jonymorse/SensorFusion-Models/outputs/previews/pt3-faceplate-alignment-concept.png

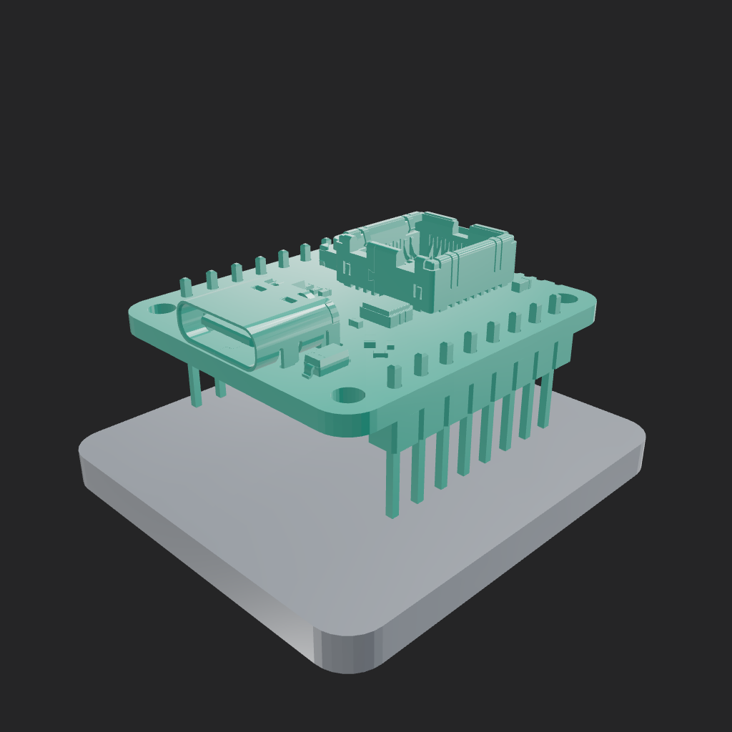
outputs/previews/pt3-faceplate-alignment-concept.png
