jonymorse/SensorFusion-Models/outputs/previews/pt3-front.png

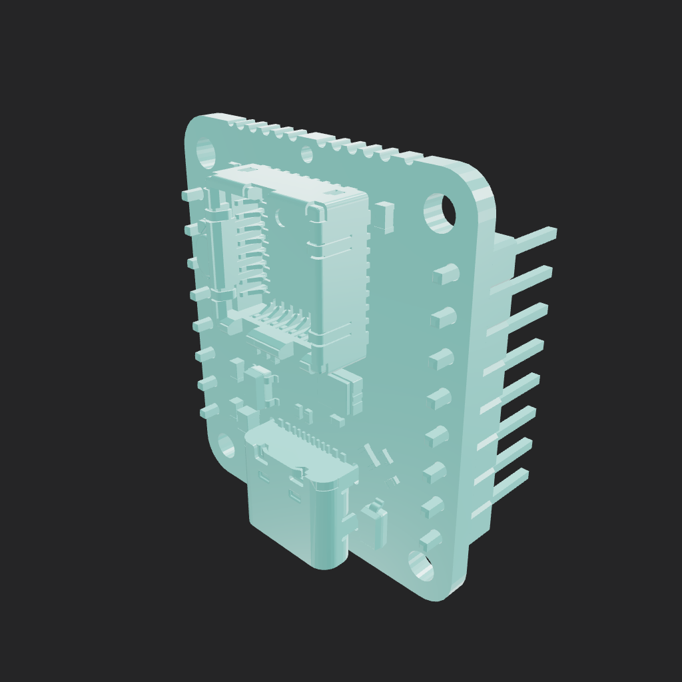
outputs/previews/pt3-front.png
