jonymorse/SensorFusion-Models/outputs/previews/pt3-right.png

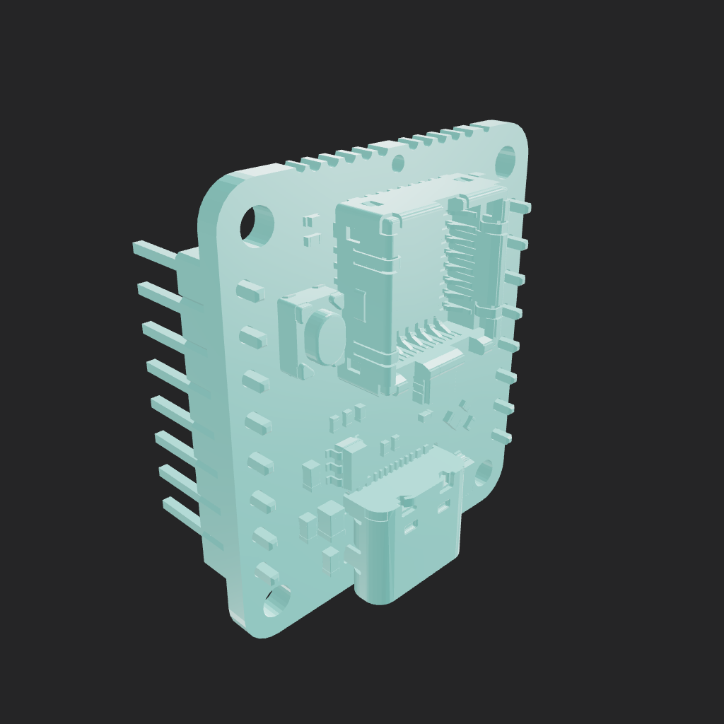
outputs/previews/pt3-right.png
