jonymorse/SensorFusion-Models/outputs/previews/pt3-top.png

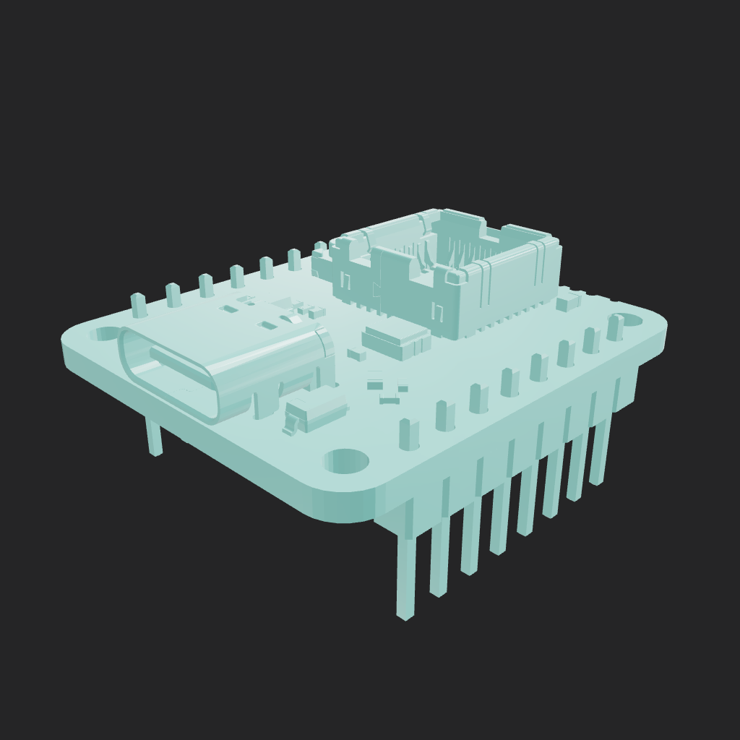
outputs/previews/pt3-top.png
