jonymorse/SensorFusion-Models/outputs/previews/purethermal-left.png

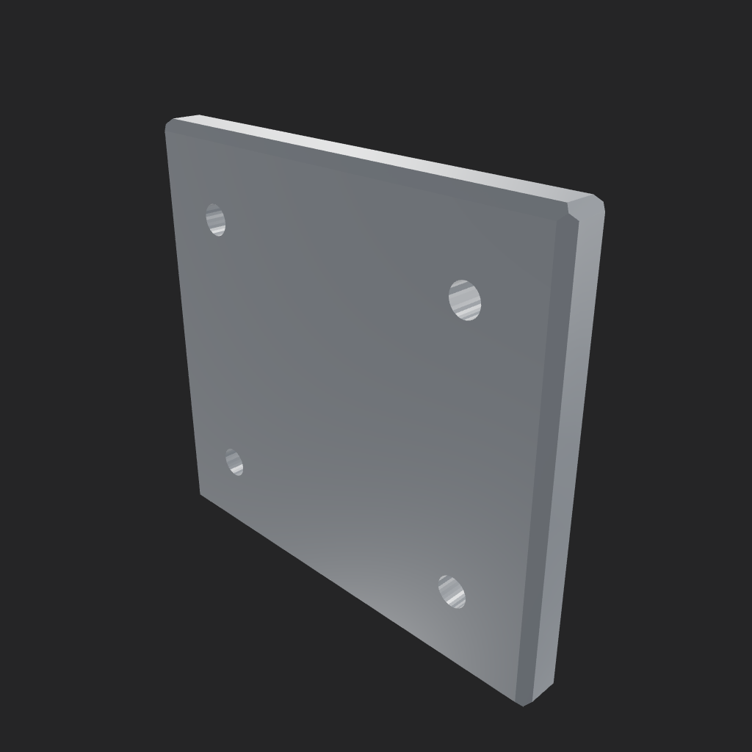
outputs/previews/purethermal-left.png
