jonymorse/SensorFusion-Models/outputs/previews/purethermal-tray-fresh.png

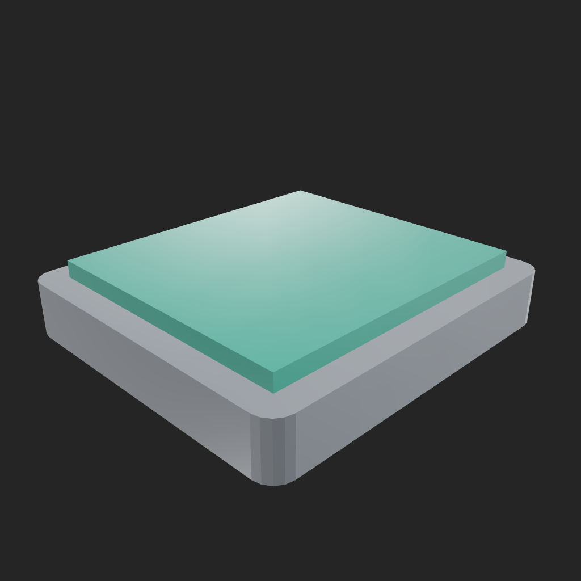
outputs/previews/purethermal-tray-fresh.png
