jonymorse/SensorFusion-Models/outputs/previews/purethermal-tray-scallop.png

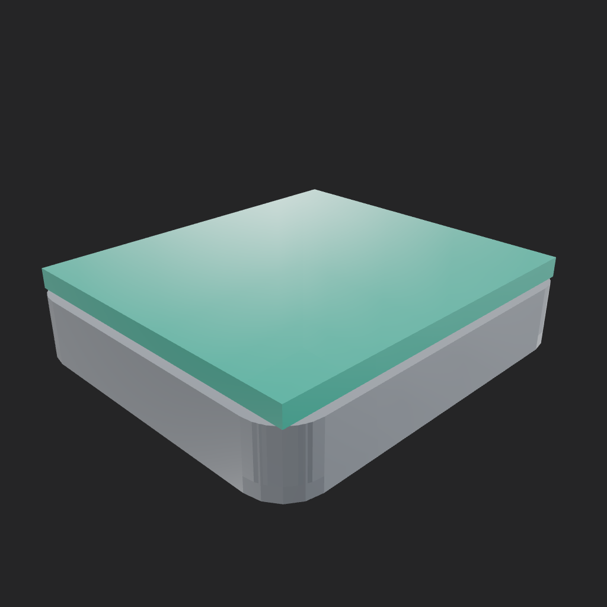
outputs/previews/purethermal-tray-scallop.png
