jonymorse/SensorFusion-Models/portfolio/assembly-viewer/models/03_pt3_slot_retainer.obj

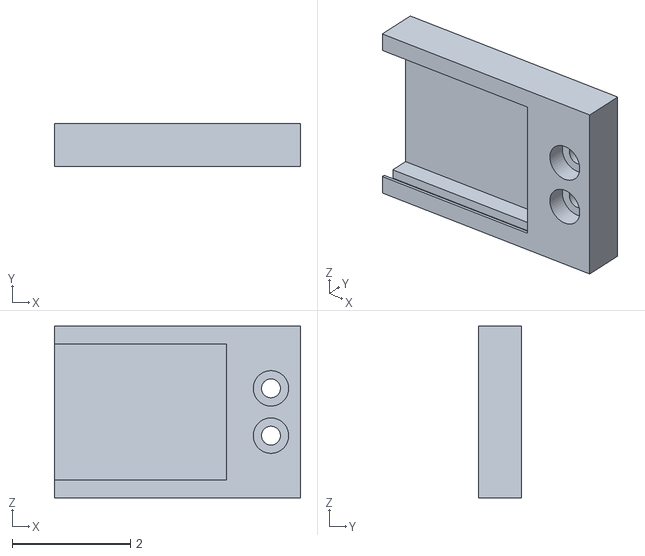
[picture p22: CAD file, 2026-07-29]
portfolio/assembly-viewer/models/03_pt3_slot_retainer.obj
4.16 x 0.72 x 2.91
