jonymorse/SensorFusion-Models/portfolio/assembly-viewer/models/08_quest_mount.obj

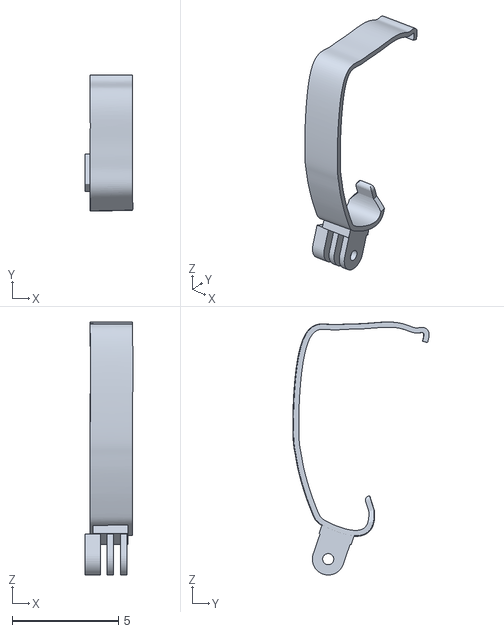
[picture p23: CAD file, 2026-07-29]
portfolio/assembly-viewer/models/08_quest_mount.obj
2.24 x 6.43 x 11.9
