jonymorse/SensorFusion-Models/portfolio/assembly-viewer/models/09_quest_3s.obj

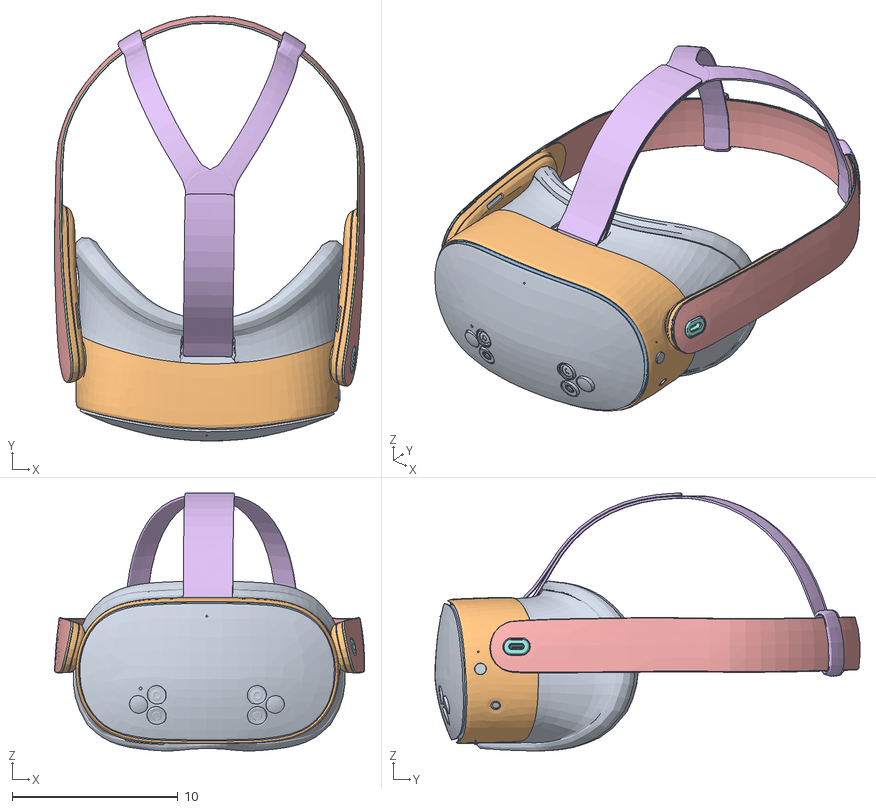
[picture p24: CAD file, 2026-07-29]
portfolio/assembly-viewer/models/09_quest_3s.obj
18.7 x 25.7 x 15.6
MeshBody12
MeshBody13
MeshBody14
MeshBody15
MeshBody16
MeshBody17
MeshBody18
MeshBody19
MeshBody20
