jonymorse/SensorFusion-Models/outputs/previews/purethermal-tray-with-pt3-step.png

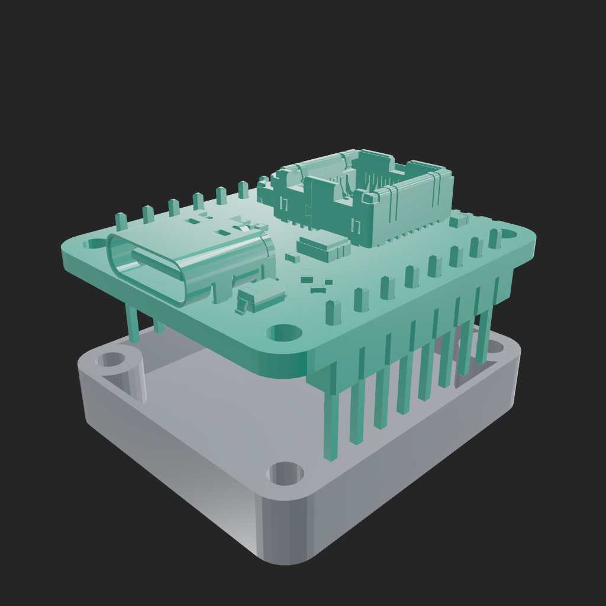
outputs/previews/purethermal-tray-with-pt3-step.png
