jonymorse/SensorFusion-Models/portfolio/assembly-viewer/dossier/integration/pt3-thermal.png

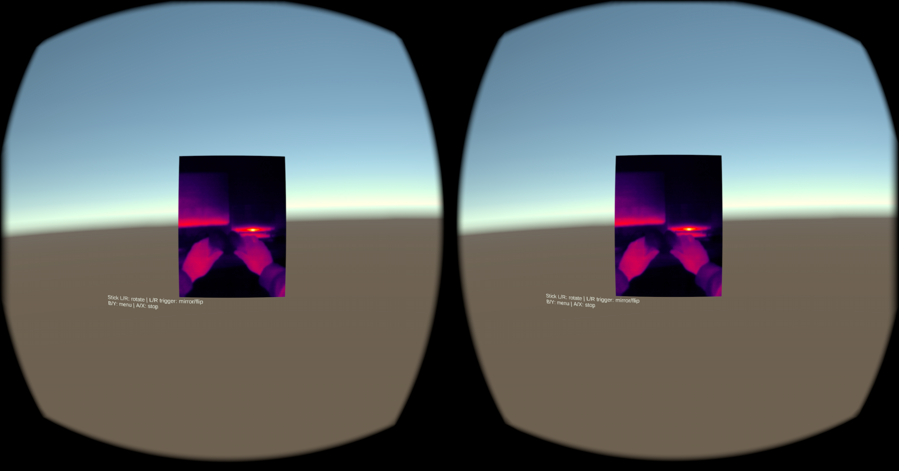
portfolio/assembly-viewer/dossier/integration/pt3-thermal.png
