jonymorse/SensorFusion-Models/portfolio/assembly-viewer/dossier/integration/realsense-depth.png

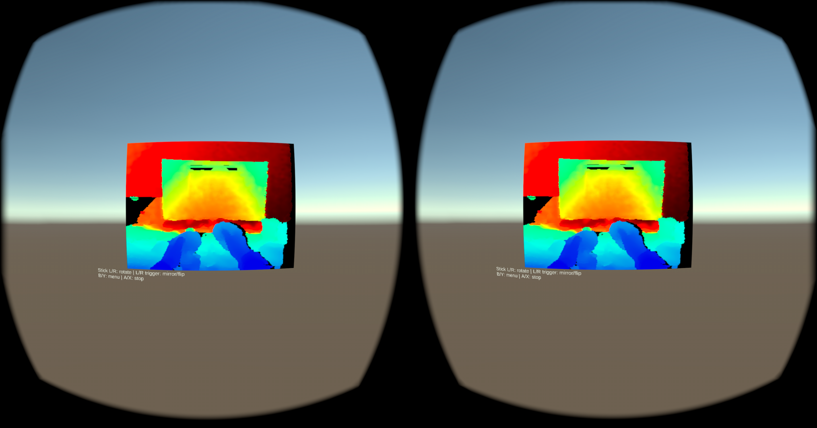
portfolio/assembly-viewer/dossier/integration/realsense-depth.png
