jonymorse/SensorFusion-Models/portfolio/assembly-viewer/dossier/integration/sensor-menu.jpg

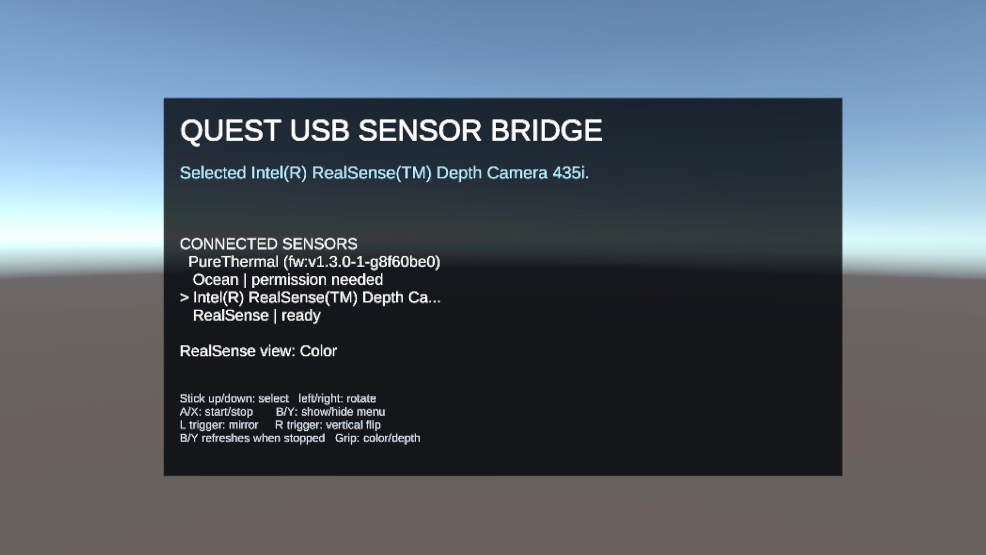
portfolio/assembly-viewer/dossier/integration/sensor-menu.jpg
