jonymorse/SensorFusion-Models/portfolio/assembly-viewer/dossier/quest-3s-reference-preview.png

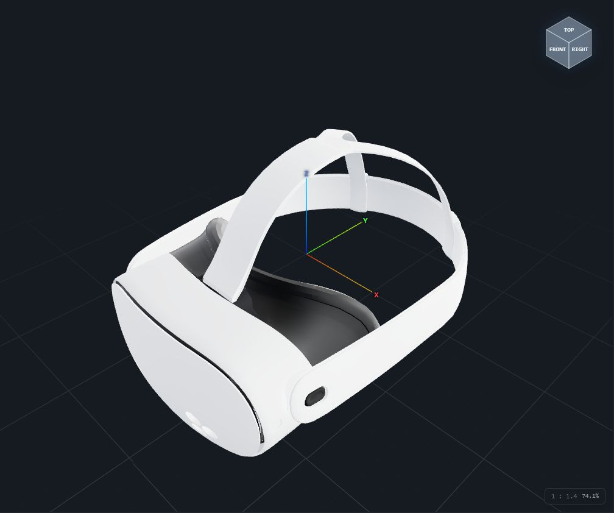
portfolio/assembly-viewer/dossier/quest-3s-reference-preview.png
