jonymorse/SensorFusion-Models/portfolio/assembly-viewer/dossier/quest-captures/latest-unity-capture.jpg

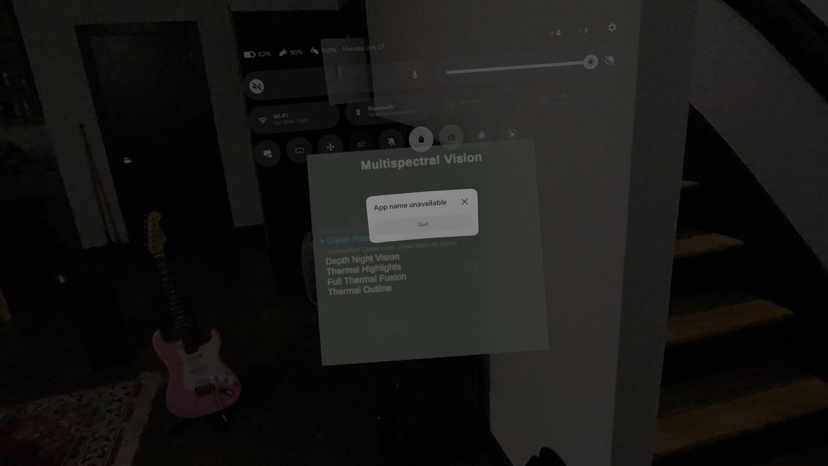
portfolio/assembly-viewer/dossier/quest-captures/latest-unity-capture.jpg
