jonymorse/SensorFusion-Models/portfolio/assembly-viewer/dossier/quest-captures/mode-02-thermal-toggle.jpg

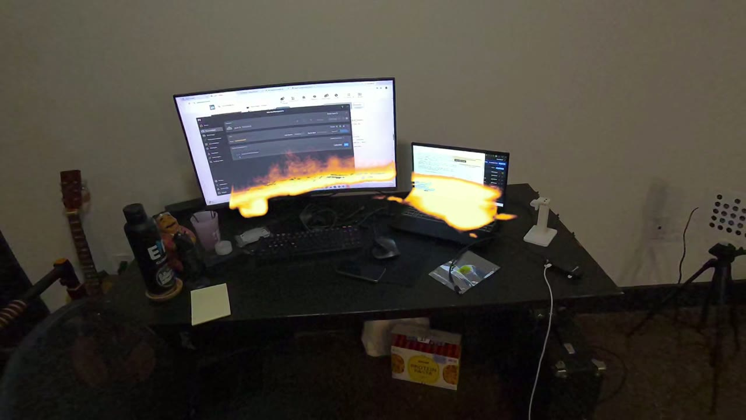
portfolio/assembly-viewer/dossier/quest-captures/mode-02-thermal-toggle.jpg
