jonymorse/SensorFusion-Models/portfolio/assembly-viewer/dossier/quest-captures/sensor-view-02.jpg

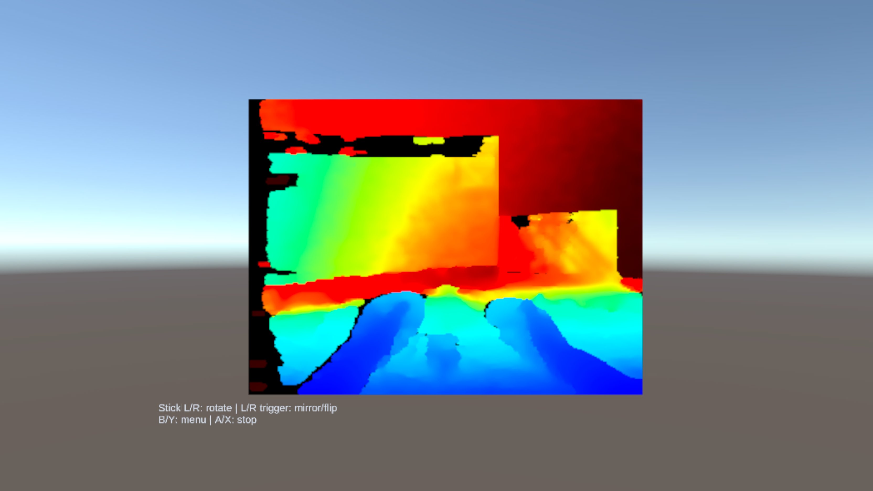
portfolio/assembly-viewer/dossier/quest-captures/sensor-view-02.jpg
