jonymorse/SensorFusion-Models/portfolio/assembly-viewer/dossier/quest-captures/sensor-view-04.jpg

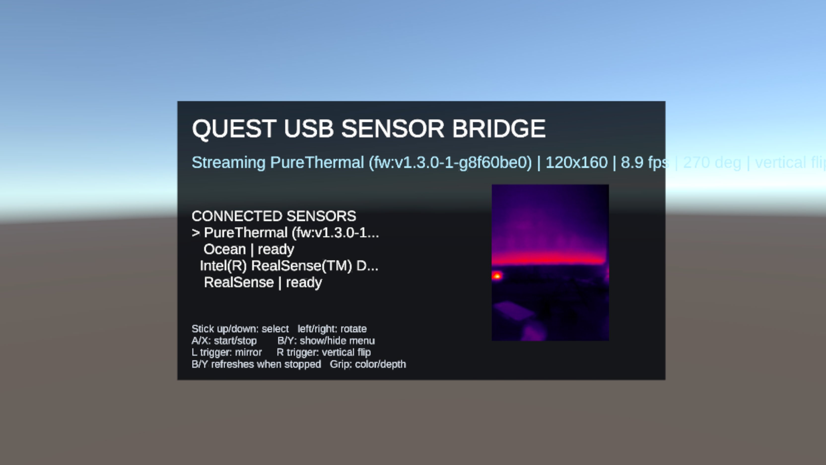
portfolio/assembly-viewer/dossier/quest-captures/sensor-view-04.jpg
