jonymorse/SensorFusion-Models/portfolio/assembly-viewer/dossier/quest-screenshot-latest.jpg

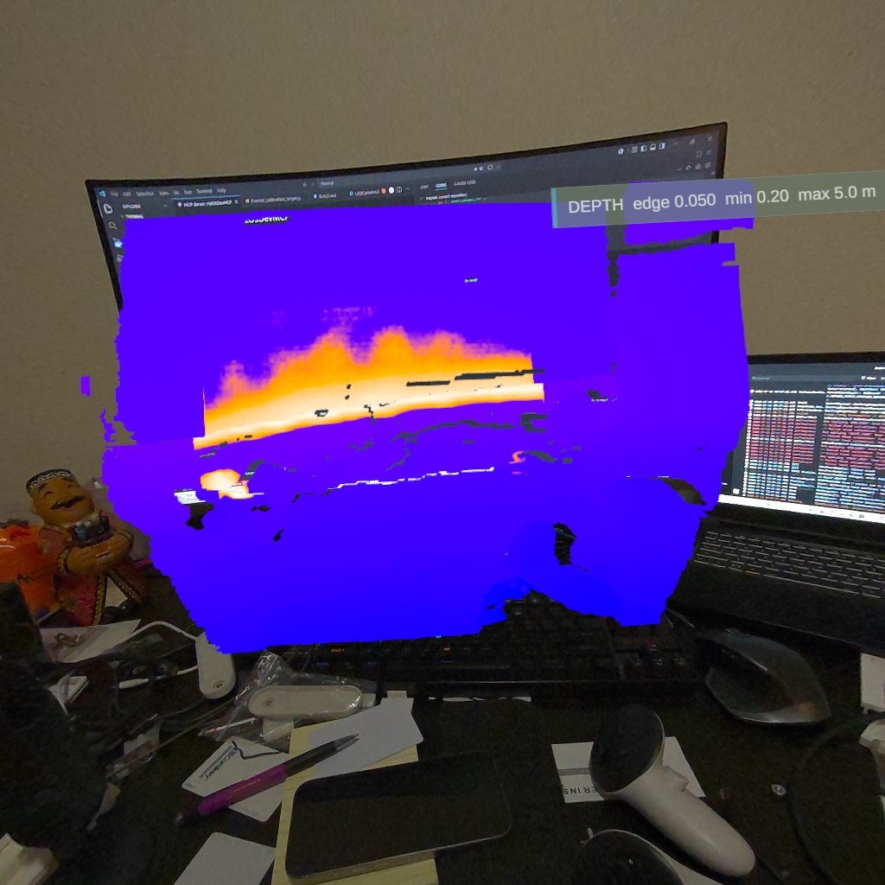
portfolio/assembly-viewer/dossier/quest-screenshot-latest.jpg
