jonymorse/SensorFusion-Models/portfolio/assembly-viewer/dossier/sensor-fusion-mount-preview.png

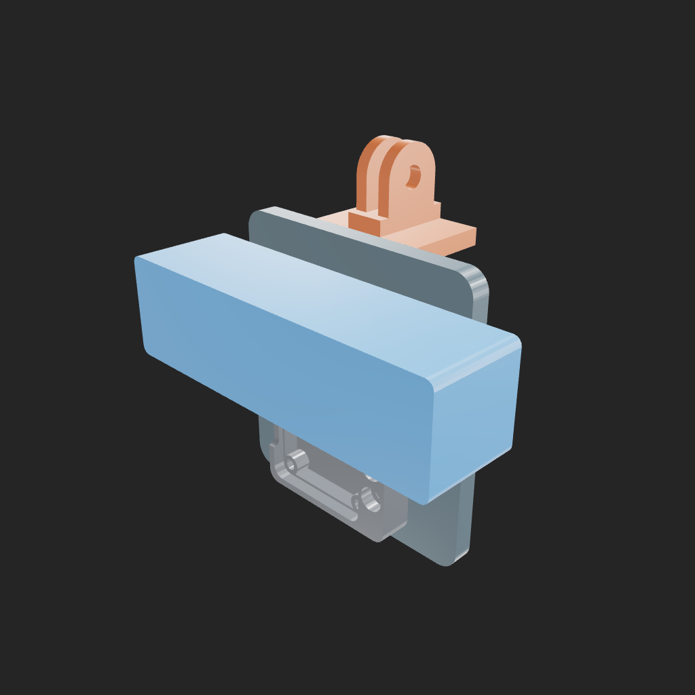
portfolio/assembly-viewer/dossier/sensor-fusion-mount-preview.png
