jonymorse/SensorFusion-Models/portfolio/assembly-viewer/dossier/calibration-after.jpg

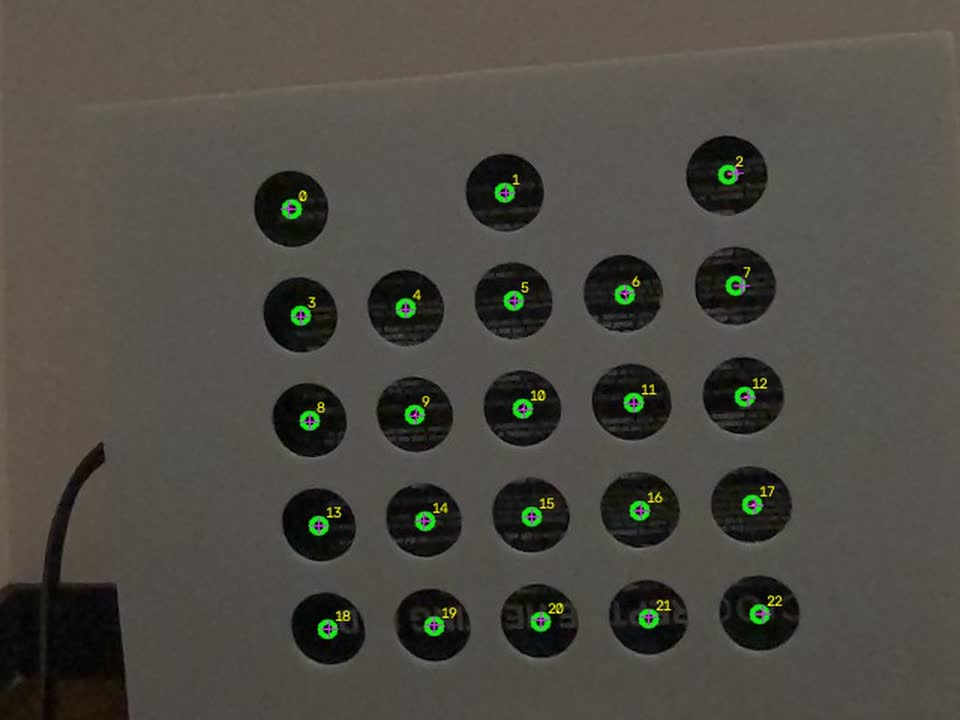
portfolio/assembly-viewer/dossier/calibration-after.jpg
