jonymorse/SensorFusion-Models/portfolio/assembly-viewer/dossier/calibration-before.jpg

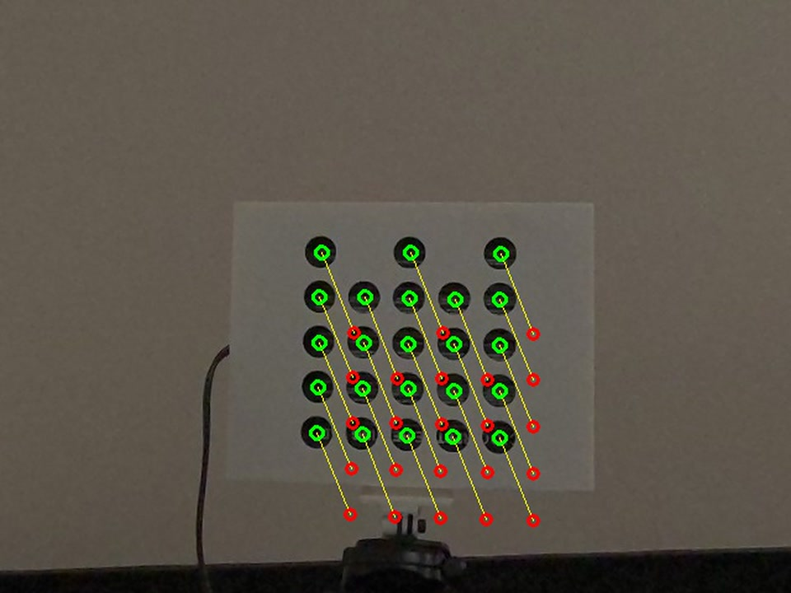
portfolio/assembly-viewer/dossier/calibration-before.jpg
