jonymorse/SensorFusion-Models/portfolio/assembly-viewer/dossier/calibration-contact-sheet.png

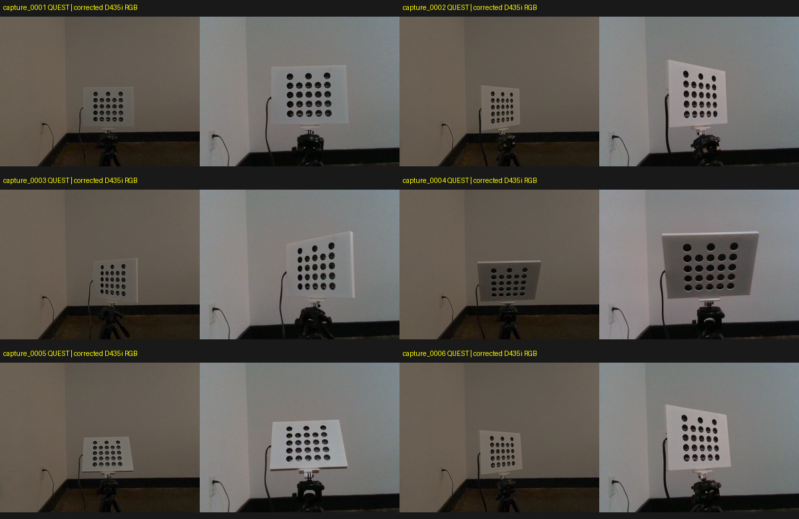
portfolio/assembly-viewer/dossier/calibration-contact-sheet.png
