jonymorse/SensorFusion-Models/portfolio/assembly-viewer/dossier/calibration/cover-poses/01-rgb.webp

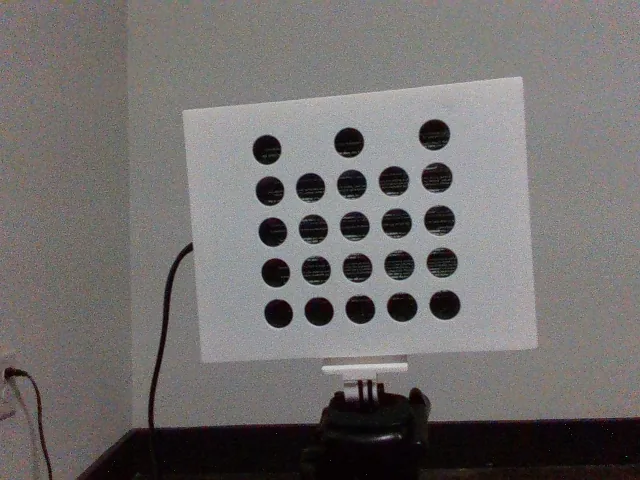
portfolio/assembly-viewer/dossier/calibration/cover-poses/01-rgb.webp
