jonymorse/SensorFusion-Models/portfolio/assembly-viewer/dossier/calibration/cover-poses/01-thermal.png

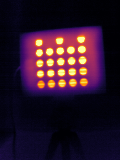
portfolio/assembly-viewer/dossier/calibration/cover-poses/01-thermal.png
