jonymorse/SensorFusion-Models/portfolio/assembly-viewer/dossier/calibration/cover-poses/06-rgb.webp

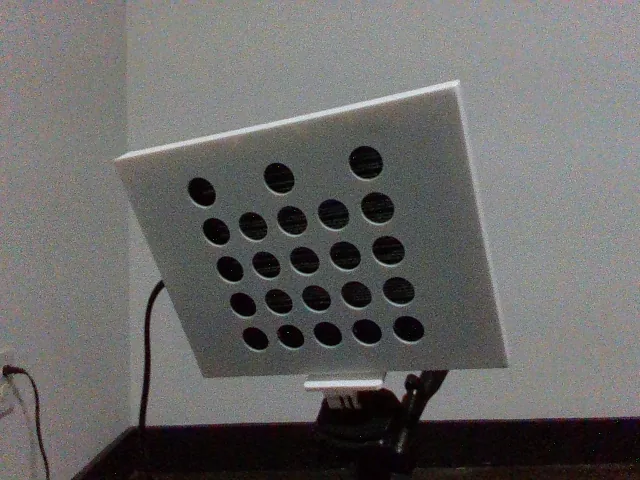
portfolio/assembly-viewer/dossier/calibration/cover-poses/06-rgb.webp
