jonymorse/SensorFusion-Models/portfolio/assembly-viewer/dossier/calibration/cover-poses/06-thermal.png

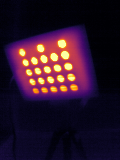
portfolio/assembly-viewer/dossier/calibration/cover-poses/06-thermal.png
