jonymorse/SensorFusion-Models/portfolio/assembly-viewer/dossier/calibration/cover-poses/07-rgb.webp

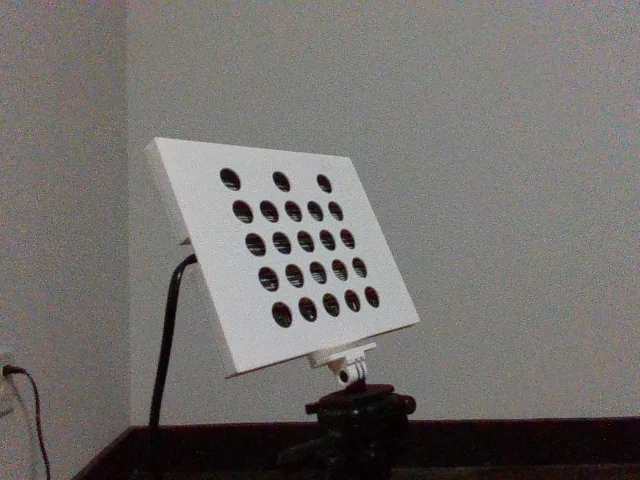
portfolio/assembly-viewer/dossier/calibration/cover-poses/07-rgb.webp
