jonymorse/SensorFusion-Models/portfolio/assembly-viewer/dossier/calibration/cover-poses/12-rgb.webp

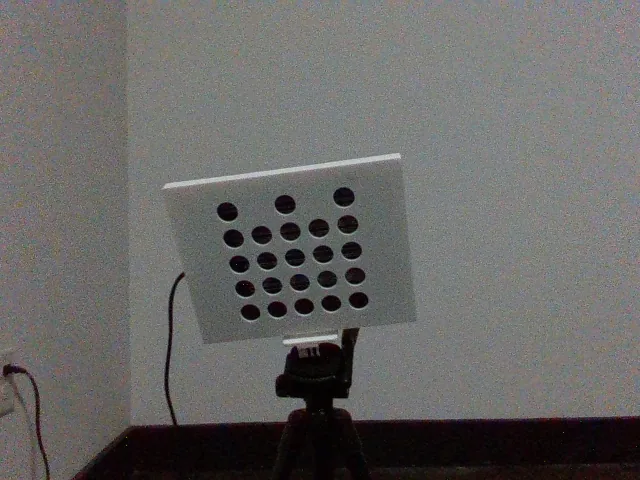
portfolio/assembly-viewer/dossier/calibration/cover-poses/12-rgb.webp
