jonymorse/SensorFusion-Models/portfolio/assembly-viewer/dossier/calibration/cover-poses/12-thermal.png

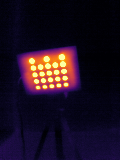
portfolio/assembly-viewer/dossier/calibration/cover-poses/12-thermal.png
