jonymorse/SensorFusion-Models/portfolio/assembly-viewer/dossier/calibration/cover-poses/16-rgb.webp

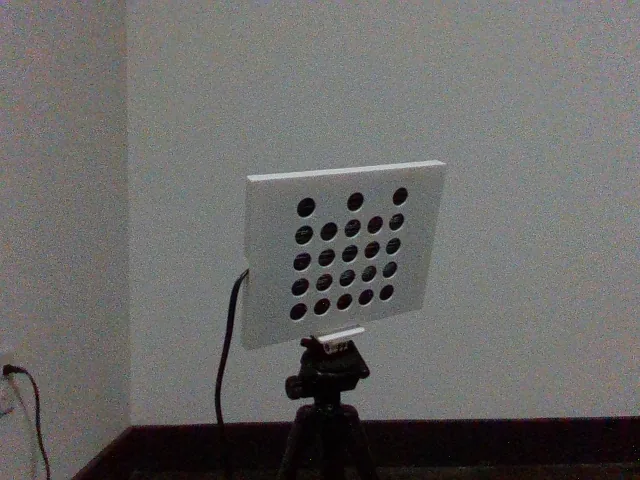
portfolio/assembly-viewer/dossier/calibration/cover-poses/16-rgb.webp
