jonymorse/SensorFusion-Models/portfolio/assembly-viewer/dossier/calibration/cover-poses/16-thermal.png

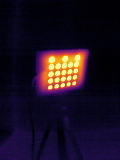
portfolio/assembly-viewer/dossier/calibration/cover-poses/16-thermal.png
