jonymorse/SensorFusion-Models/portfolio/assembly-viewer/dossier/calibration/cover-poses/18-rgb.webp

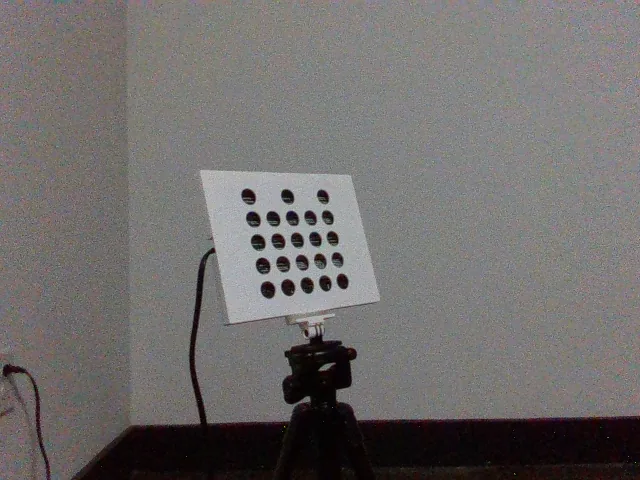
portfolio/assembly-viewer/dossier/calibration/cover-poses/18-rgb.webp
