jonymorse/SensorFusion-Models/portfolio/assembly-viewer/dossier/calibration/cover-poses/18-thermal.png

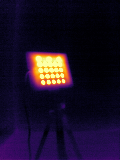
portfolio/assembly-viewer/dossier/calibration/cover-poses/18-thermal.png
