jonymorse/SensorFusion-Models/portfolio/assembly-viewer/dossier/calibration/cover-poses/24-rgb.webp

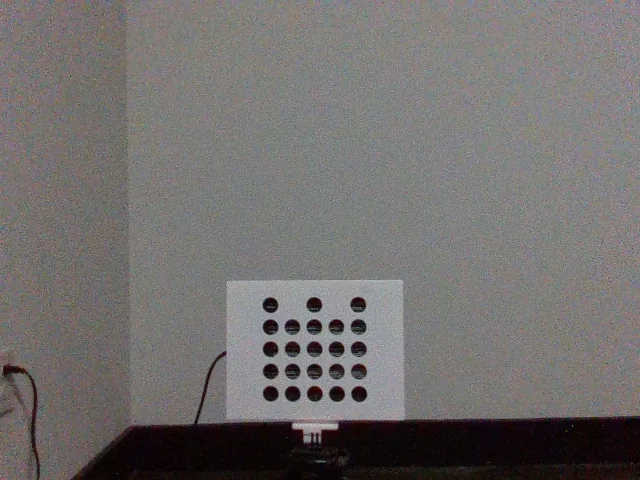
portfolio/assembly-viewer/dossier/calibration/cover-poses/24-rgb.webp
