jonymorse/SensorFusion-Models/portfolio/assembly-viewer/dossier/calibration/cover-poses/24-thermal.png

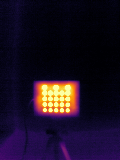
portfolio/assembly-viewer/dossier/calibration/cover-poses/24-thermal.png
