jonymorse/SensorFusion-Models/portfolio/assembly-viewer/dossier/calibration/cover-poses/31-rgb.webp

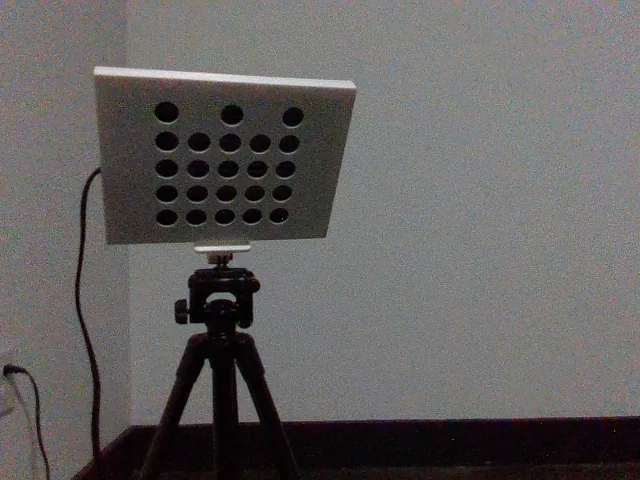
portfolio/assembly-viewer/dossier/calibration/cover-poses/31-rgb.webp
