jonymorse/SensorFusion-Models/portfolio/assembly-viewer/dossier/calibration/cover-poses/31-thermal.png

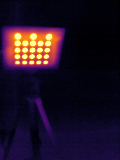
portfolio/assembly-viewer/dossier/calibration/cover-poses/31-thermal.png
