jonymorse/SensorFusion-Models/portfolio/assembly-viewer/dossier/calibration/pt3-full-solver-diagnostics.jpg

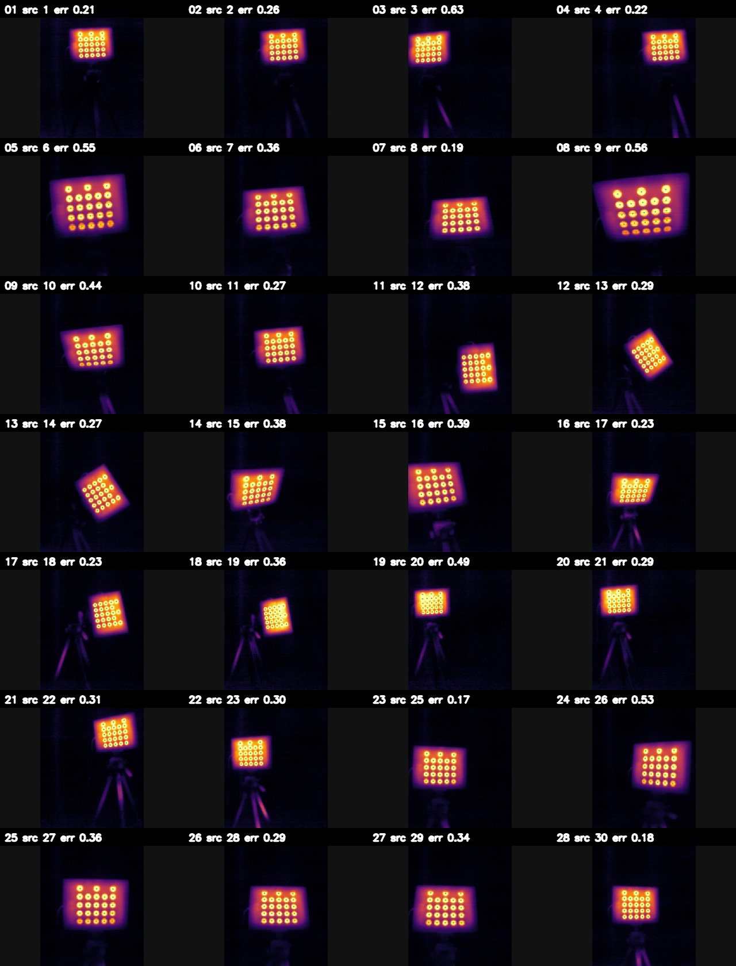
portfolio/assembly-viewer/dossier/calibration/pt3-full-solver-diagnostics.jpg
