jonymorse/SensorFusion-Models/portfolio/assembly-viewer/dossier/calibration/pt3-pose-sweep.jpg

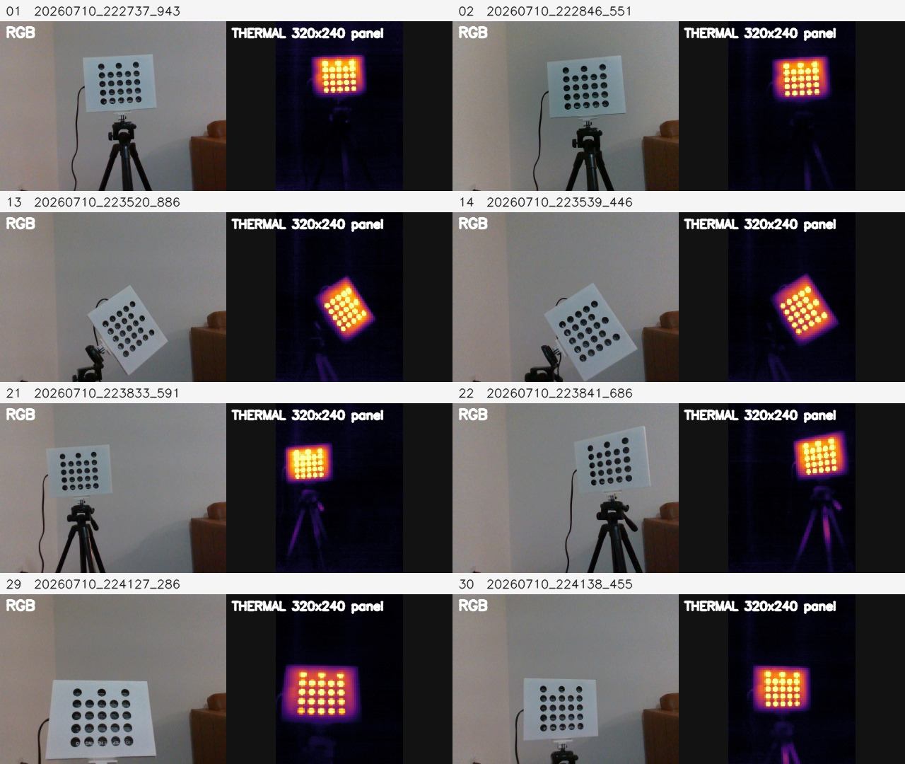
portfolio/assembly-viewer/dossier/calibration/pt3-pose-sweep.jpg
