jonymorse/SensorFusion-Models/portfolio/assembly-viewer/dossier/calibration/pt3-reprojection.png

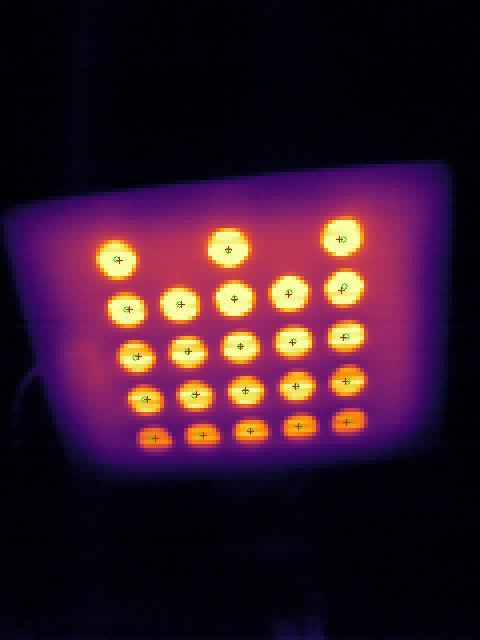
portfolio/assembly-viewer/dossier/calibration/pt3-reprojection.png
