jonymorse/SensorFusion-Models/portfolio/assembly-viewer/dossier/calibration/quest-before-after.jpg

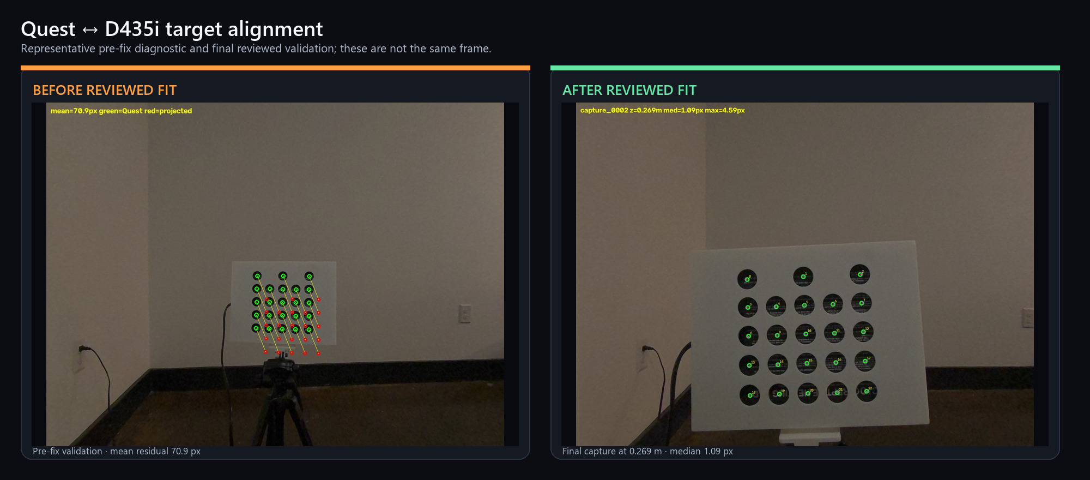
portfolio/assembly-viewer/dossier/calibration/quest-before-after.jpg
