jonymorse/SensorFusion-Models/portfolio/assembly-viewer/dossier/calibration/quest-correspondence-review.png

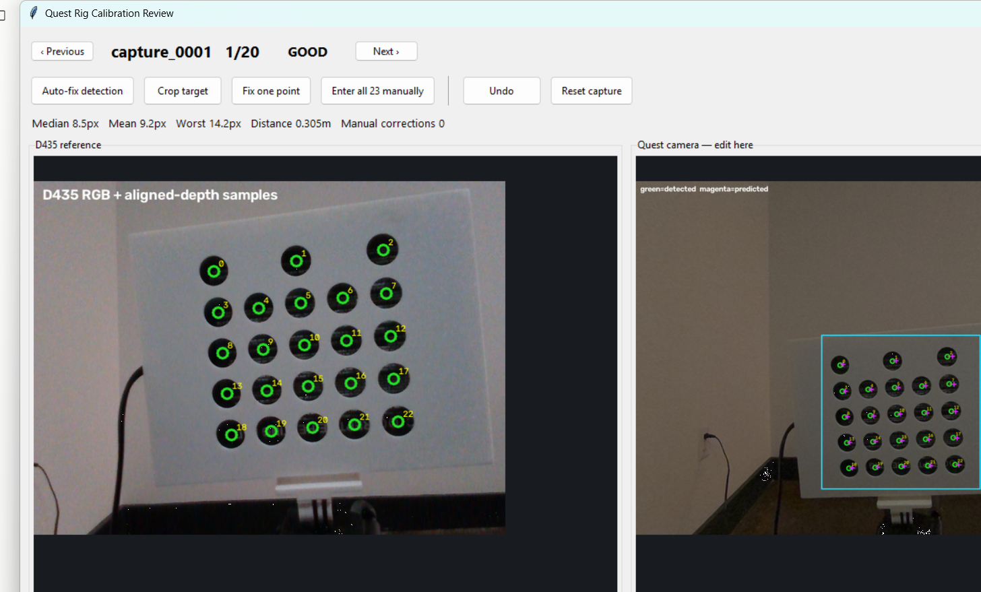
portfolio/assembly-viewer/dossier/calibration/quest-correspondence-review.png
