jonymorse/SensorFusion-Models/portfolio/assembly-viewer/dossier/calibration/quest-final-validation.jpg

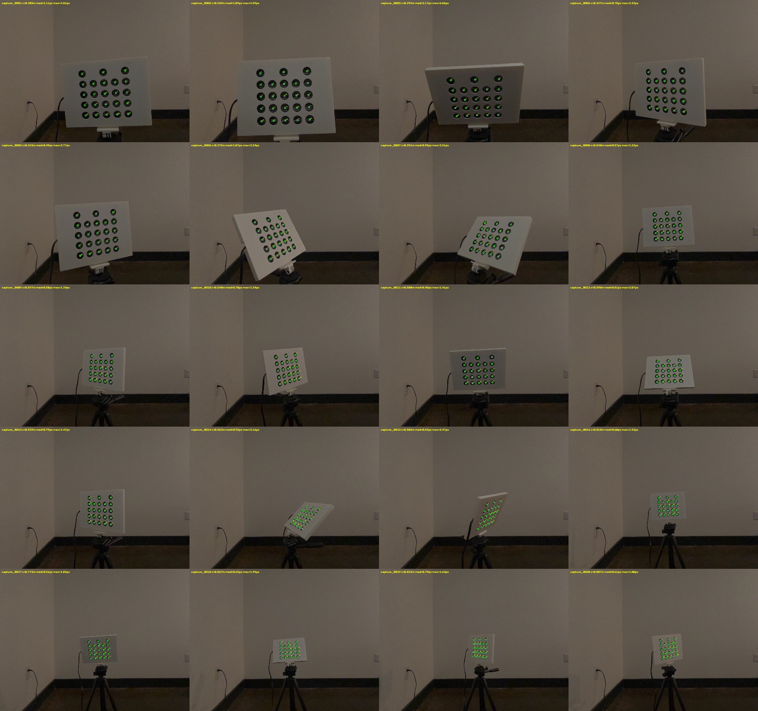
portfolio/assembly-viewer/dossier/calibration/quest-final-validation.jpg
