jonymorse/SensorFusion-Models/portfolio/assembly-viewer/dossier/calibration/sensor-capture-triplet.png

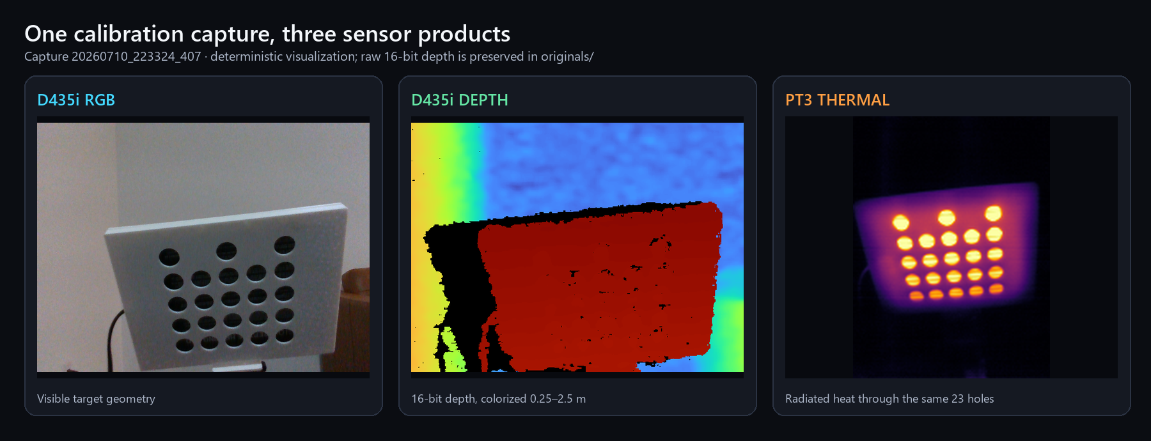
portfolio/assembly-viewer/dossier/calibration/sensor-capture-triplet.png
