jonymorse/SensorFusion-Models/portfolio/assembly-viewer/dossier/calibration/session-20260729/capture-sweep.jpg

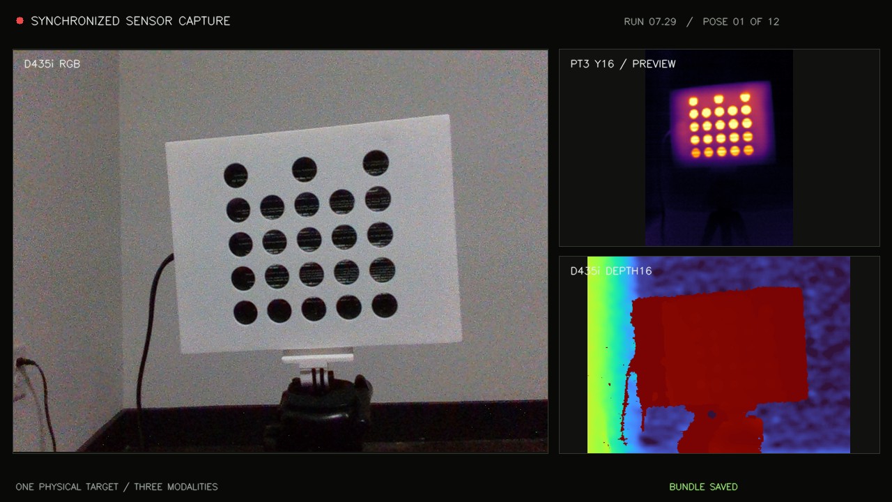
portfolio/assembly-viewer/dossier/calibration/session-20260729/capture-sweep.jpg
