jonymorse/SensorFusion-Models/portfolio/assembly-viewer/dossier/calibration/session-20260729/correspondence-review.jpg

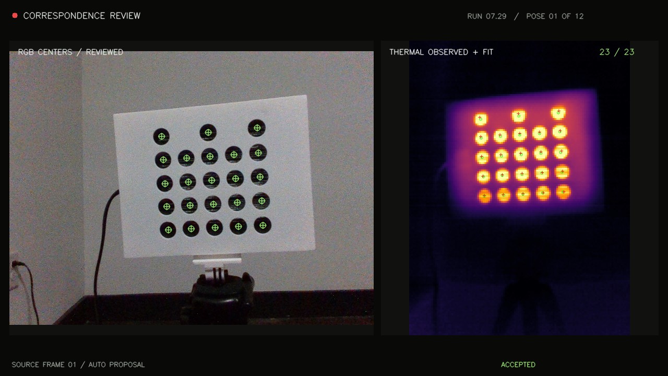
portfolio/assembly-viewer/dossier/calibration/session-20260729/correspondence-review.jpg
