jonymorse/SensorFusion-Models/portfolio/assembly-viewer/dossier/calibration/session-20260729/live-fusion-dashboard.jpg

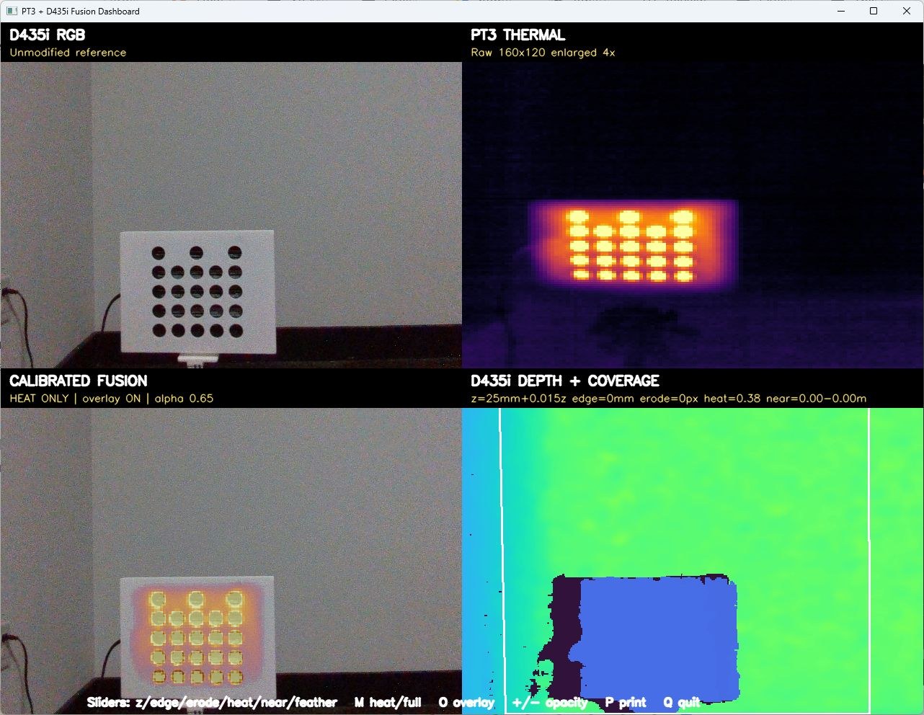
portfolio/assembly-viewer/dossier/calibration/session-20260729/live-fusion-dashboard.jpg
