jonymorse/SensorFusion-Models/portfolio/assembly-viewer/dossier/calibration/session-20260729/pose-atlas.jpg

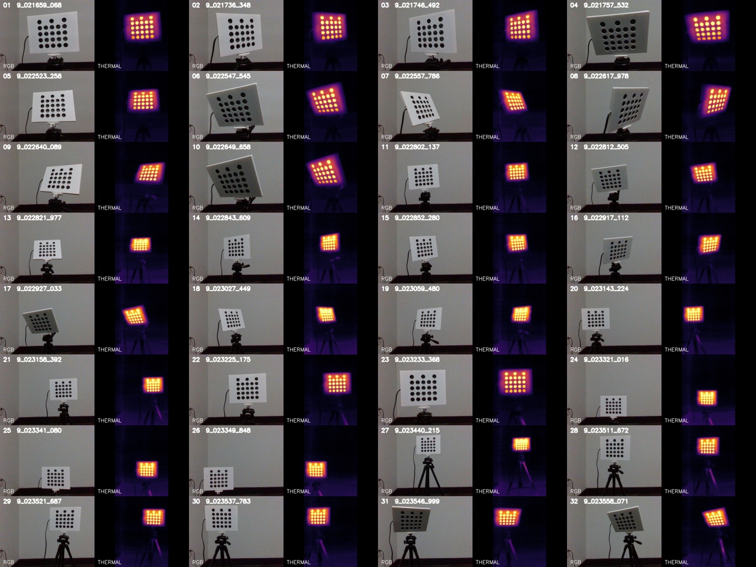
portfolio/assembly-viewer/dossier/calibration/session-20260729/pose-atlas.jpg
