jonymorse/SensorFusion-Models/portfolio/assembly-viewer/dossier/calibration/session-20260729/solver-convergence-clean.jpg

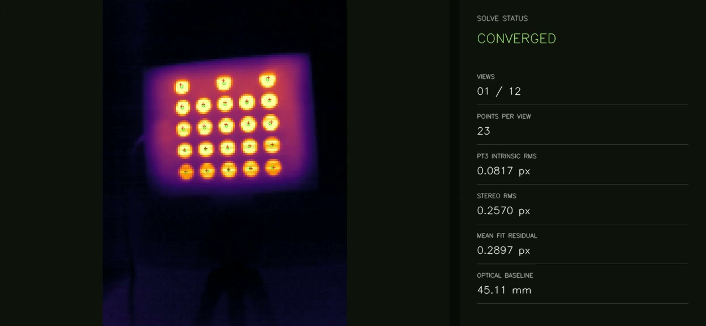
portfolio/assembly-viewer/dossier/calibration/session-20260729/solver-convergence-clean.jpg
