jonymorse/SensorFusion-Models/portfolio/assembly-viewer/dossier/calibration/session-20260729/solver-convergence.jpg

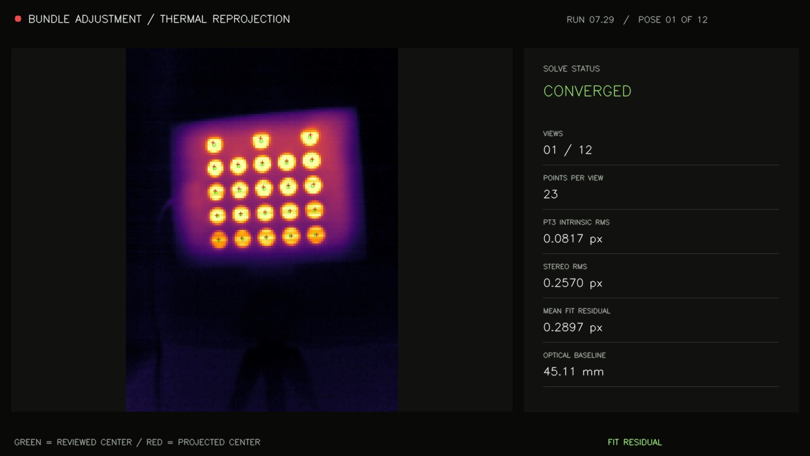
portfolio/assembly-viewer/dossier/calibration/session-20260729/solver-convergence.jpg
