jonymorse/SensorFusion-Models/portfolio/assembly-viewer/dossier/calibration/session-20260729/validation/calibrated-fusion-clean.jpg

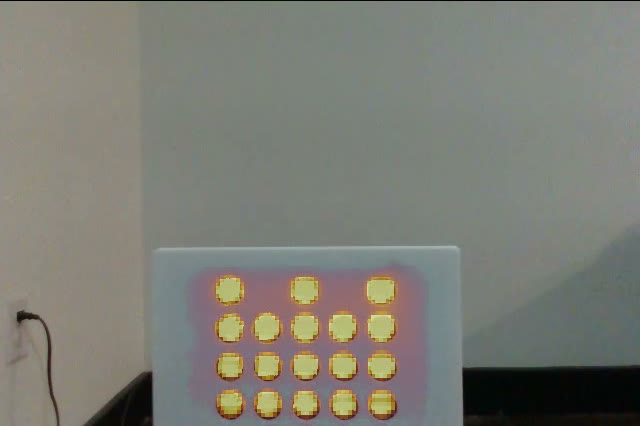
portfolio/assembly-viewer/dossier/calibration/session-20260729/validation/calibrated-fusion-clean.jpg
