jonymorse/SensorFusion-Models/portfolio/assembly-viewer/dossier/calibration/session-20260729/validation/calibrated-fusion.jpg

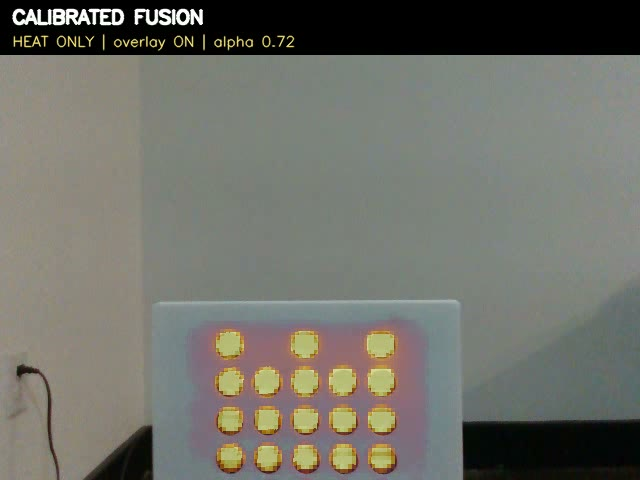
portfolio/assembly-viewer/dossier/calibration/session-20260729/validation/calibrated-fusion.jpg
