jonymorse/SensorFusion-Models/portfolio/assembly-viewer/dossier/calibration/session-20260729/validation/d435i-rgb.jpg

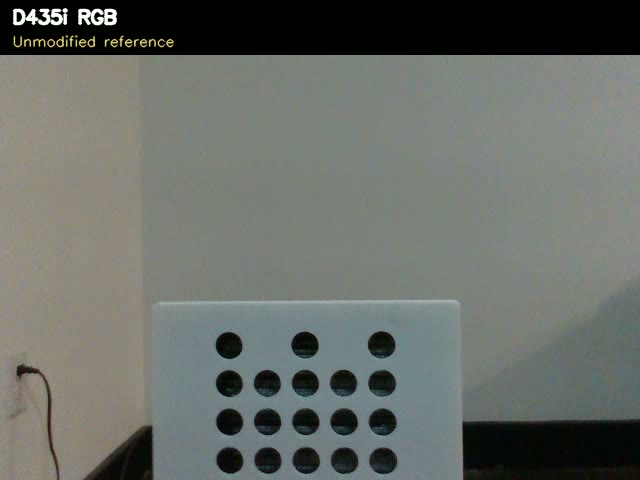
portfolio/assembly-viewer/dossier/calibration/session-20260729/validation/d435i-rgb.jpg
