jonymorse/SensorFusion-Models/portfolio/assembly-viewer/dossier/calibration/session-20260729/validation/pt3-thermal-clean.jpg

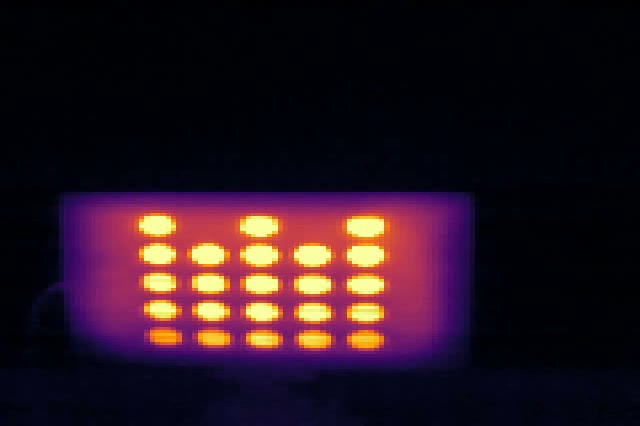
portfolio/assembly-viewer/dossier/calibration/session-20260729/validation/pt3-thermal-clean.jpg
