jonymorse/SensorFusion-Models/portfolio/assembly-viewer/dossier/calibration/session-20260729/validation/pt3-thermal.jpg

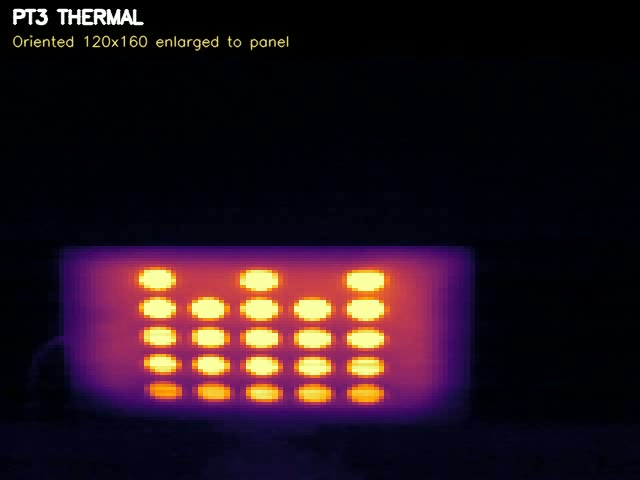
portfolio/assembly-viewer/dossier/calibration/session-20260729/validation/pt3-thermal.jpg
