jonymorse/SensorFusion-Models/portfolio/assembly-viewer/dossier/thermal-calibration-target-preview.png

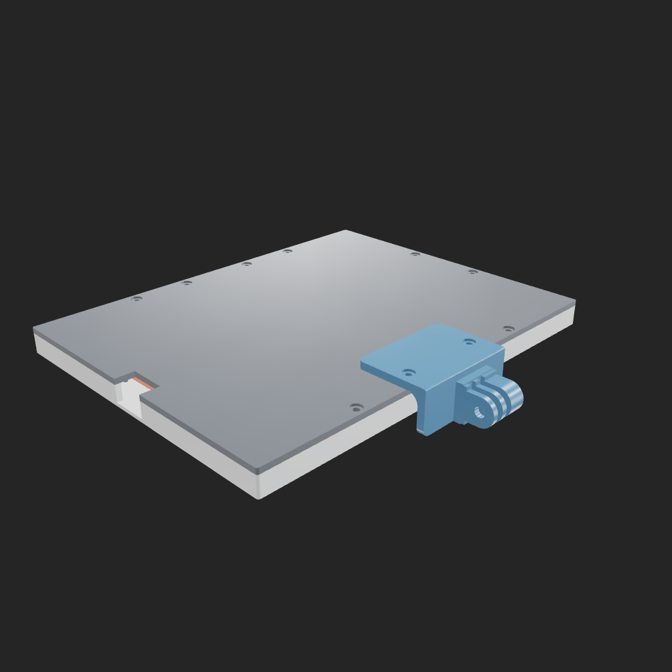
portfolio/assembly-viewer/dossier/thermal-calibration-target-preview.png
